PasseRapport/Dive_Computer/Software/DiveComputer/main/components/pressure_sensor.h

#ifndef PRESSURE_SENSOR_H
#define PRESSURE_SENSOR_H

#include <stdint.h>

// Initialise le bus I2C et configure le capteur 
void init_dive_sensor(void);
void calibrate_surface_pressure(void);
// Tâche FreeRTOS qui va lire le capteur en boucle
void dive_sensor_task(void *pvParameters);

#endif // PRESSURE_SENSOR_H
